surajjha0622/CrashLink/hardware/pcb/gateway_node/2D_gn_top_v1.png

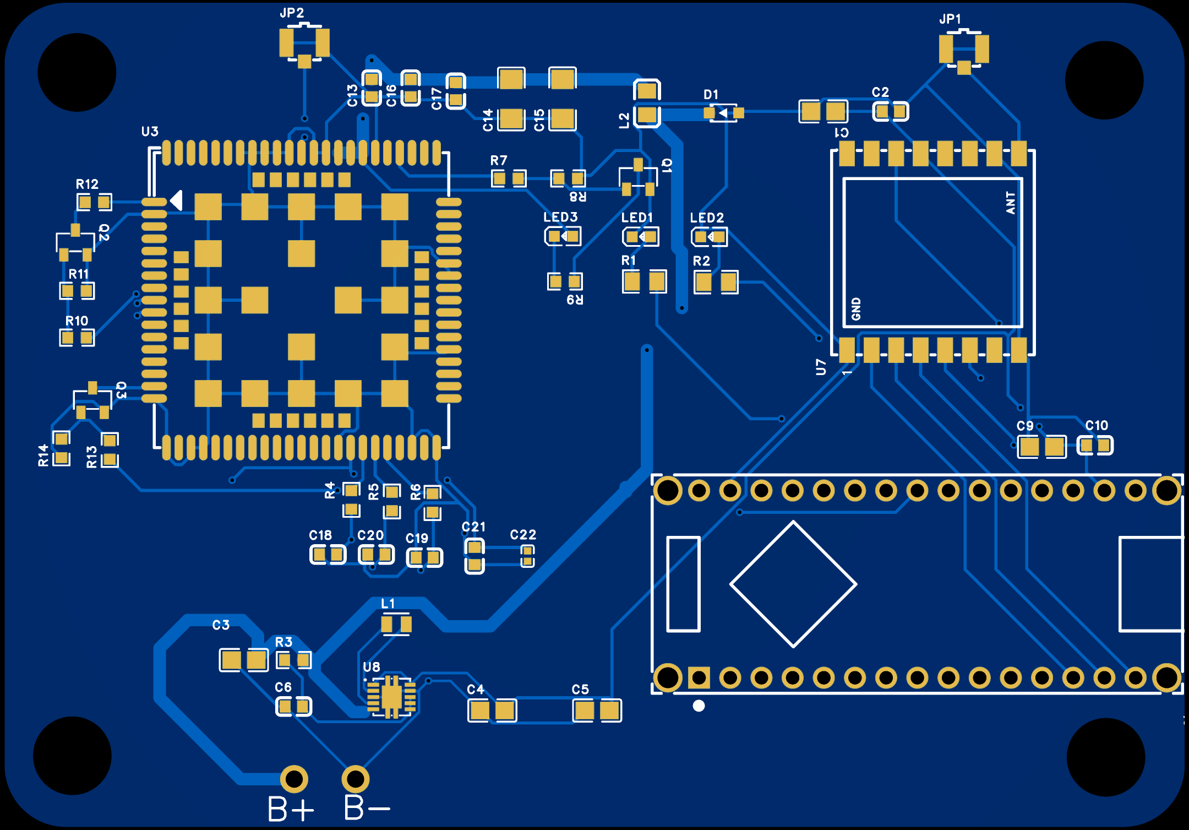
hardware/pcb/gateway_node/2D_gn_top_v1.png
