surajjha0622/CrashLink/hardware/pcb/gateway_node/3D_gn_v1.png

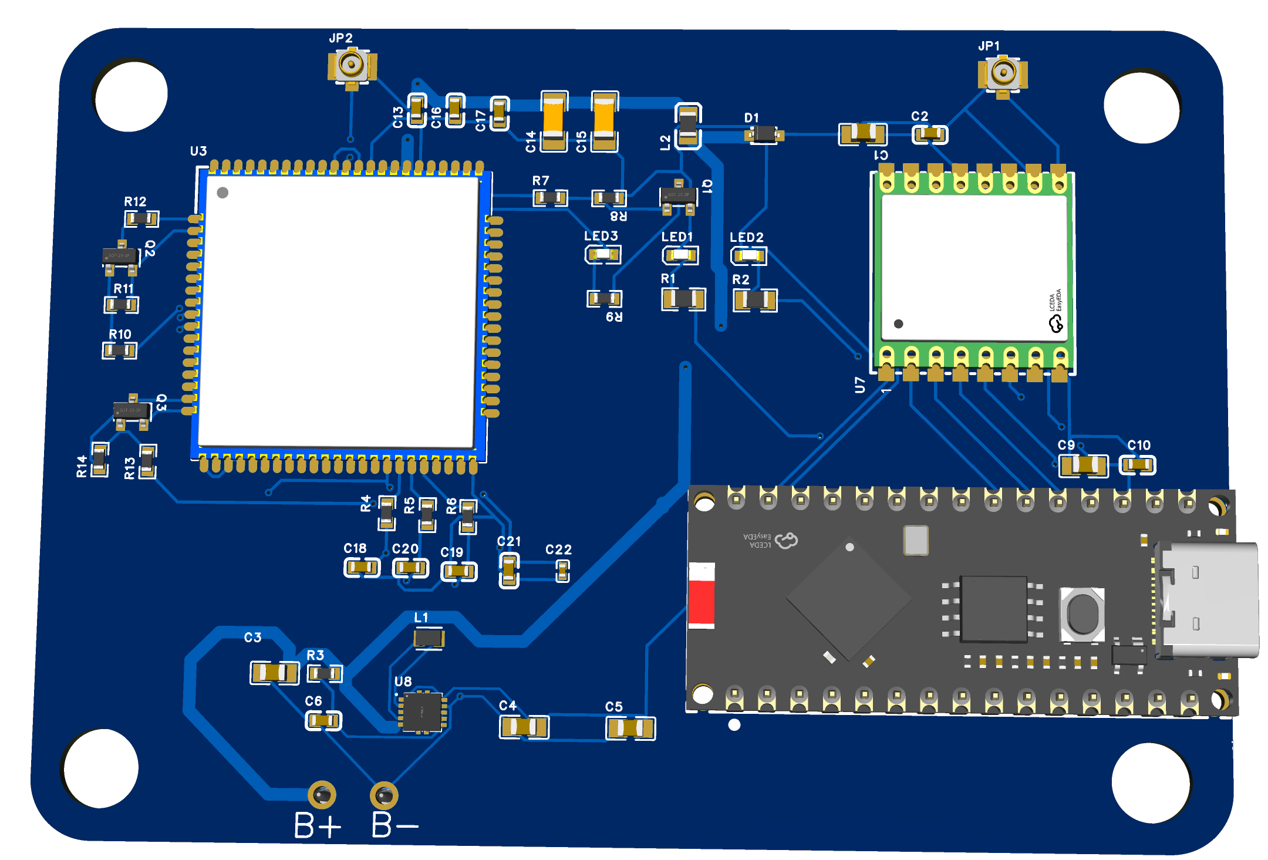
hardware/pcb/gateway_node/3D_gn_v1.png
