surajjha0622/CrashLink/hardware/pcb/gateway_node/PCB_gn_v1.png

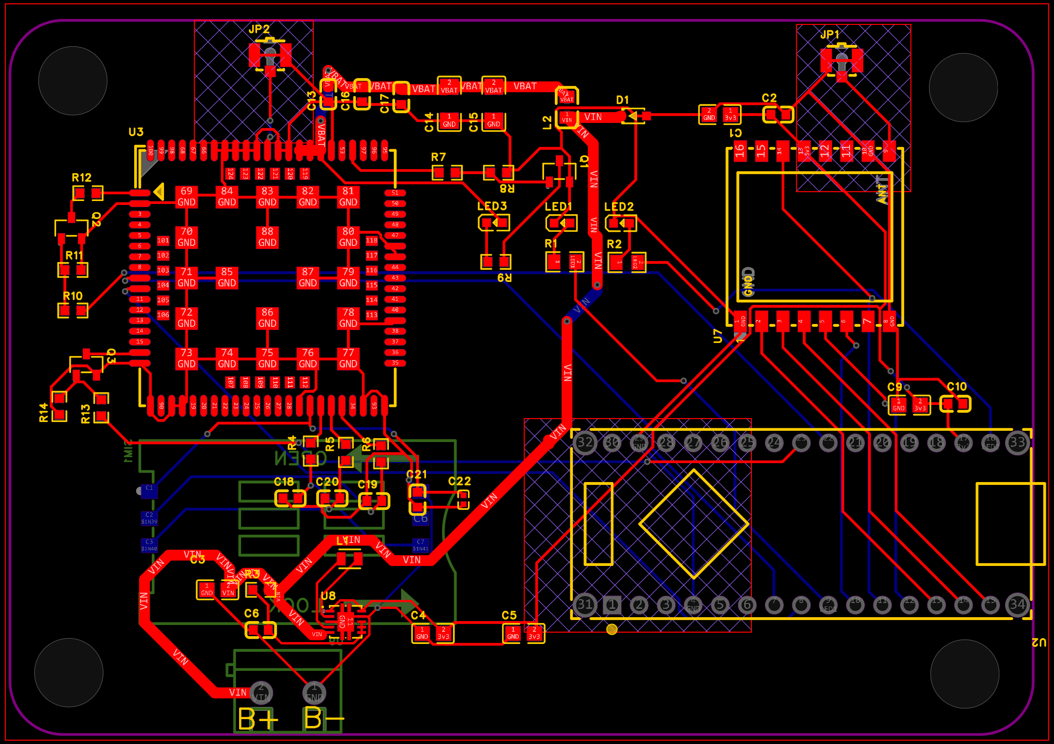
hardware/pcb/gateway_node/PCB_gn_v1.png
