surajjha0622/CrashLink/hardware/pcb/relay_node/2D_rn_bottom_v1.png

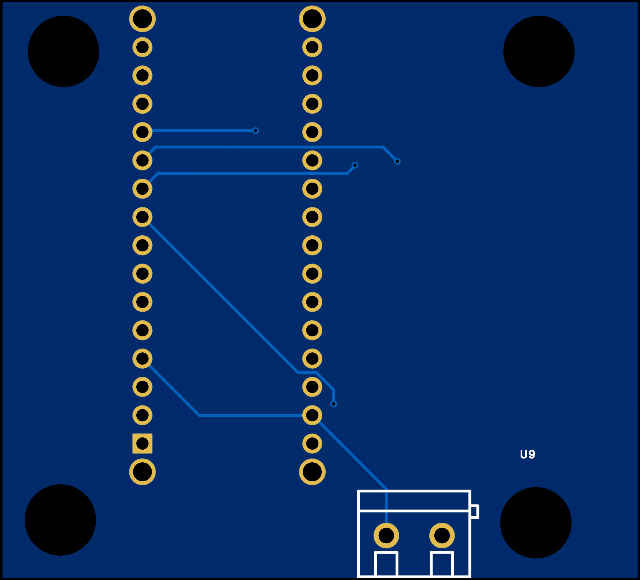
hardware/pcb/relay_node/2D_rn_bottom_v1.png
