surajjha0622/CrashLink/hardware/pcb/relay_node/3D_rn_v1.png

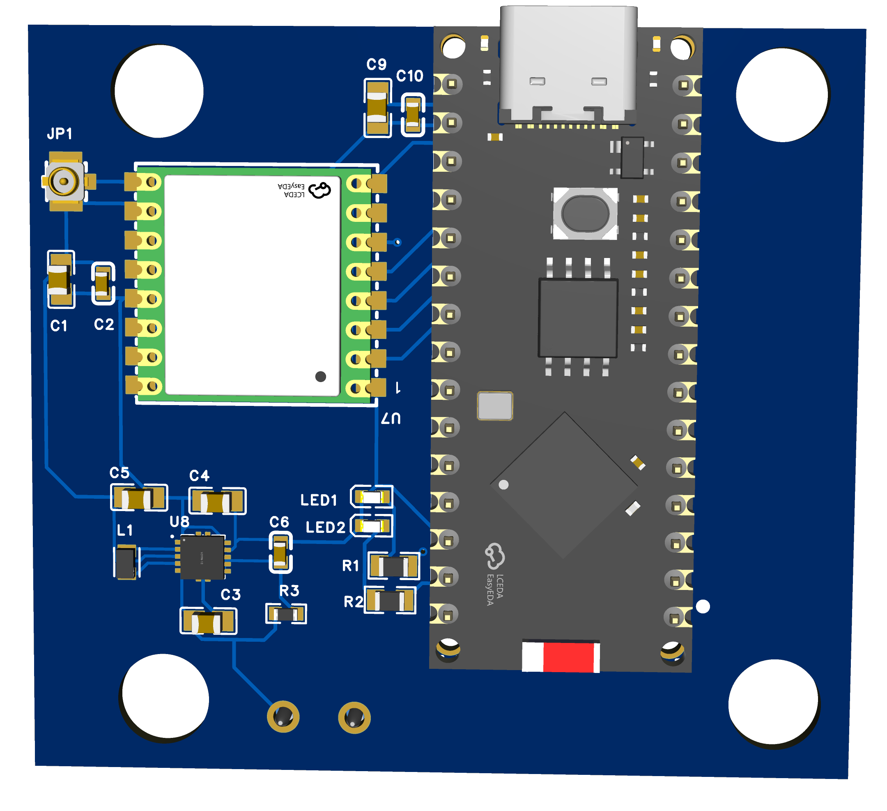
hardware/pcb/relay_node/3D_rn_v1.png
