surajjha0622/CrashLink/hardware/pcb/relay_node/SCH_rn_v1.png

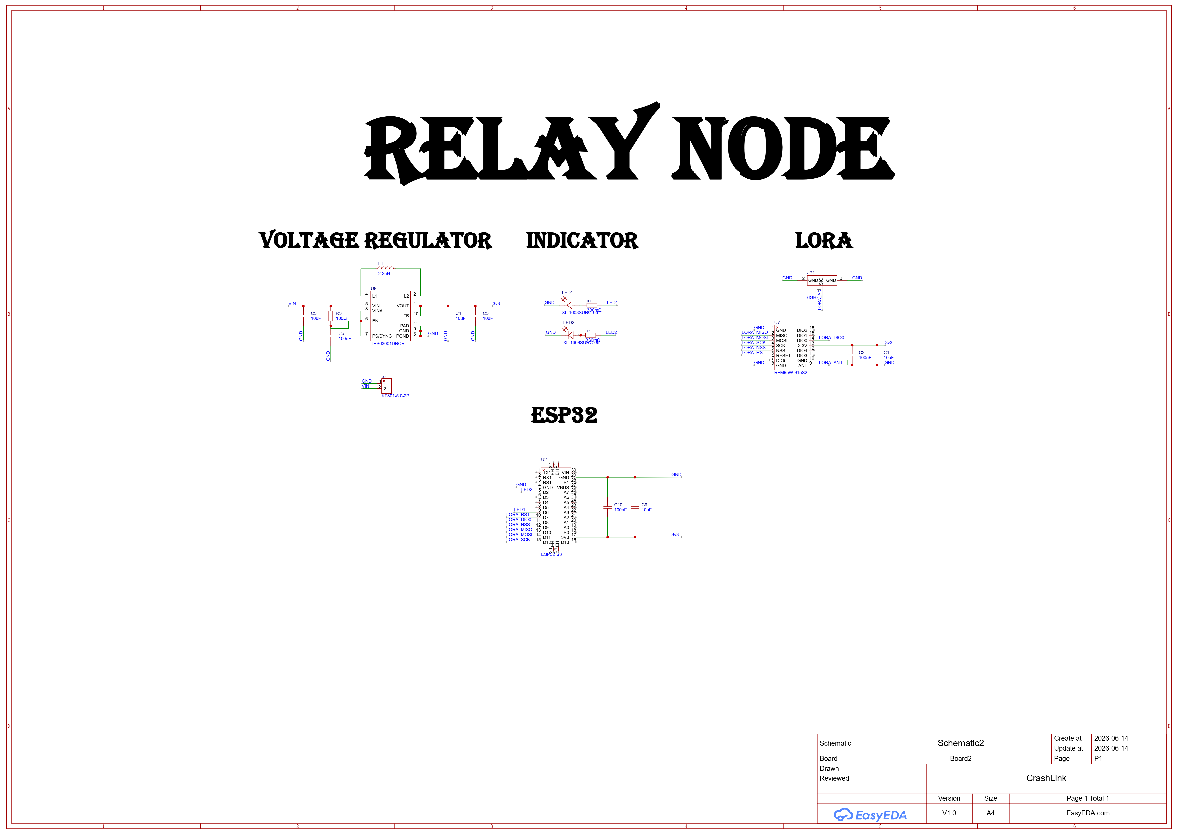
hardware/pcb/relay_node/SCH_rn_v1.png
