surajjha0622/CrashLink/hardware/pcb/vechile_node/2D_vn_top_v1.png

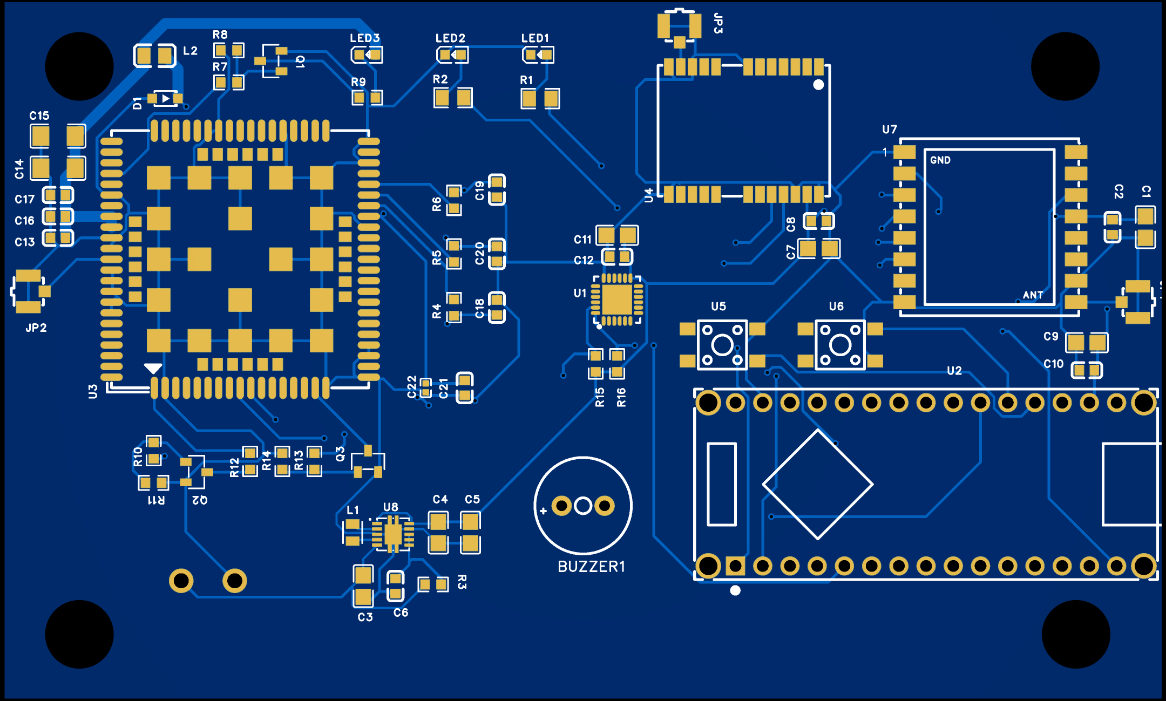
hardware/pcb/vechile_node/2D_vn_top_v1.png
