surajjha0622/CrashLink/hardware/pcb/vechile_node/3D_vn_v1.png

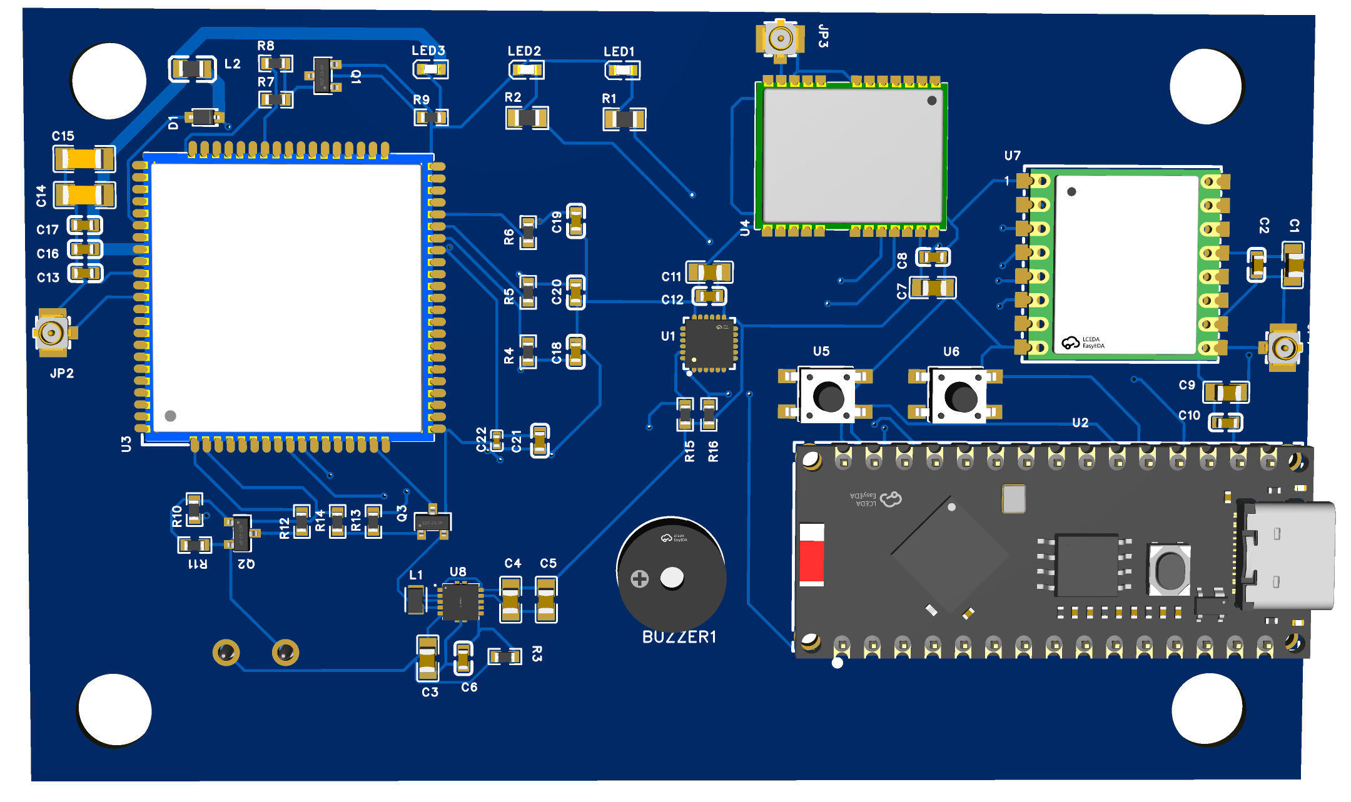
hardware/pcb/vechile_node/3D_vn_v1.png
