surajjha0622/CrashLink/hardware/pcb/vechile_node/PCB_vn_v1.png

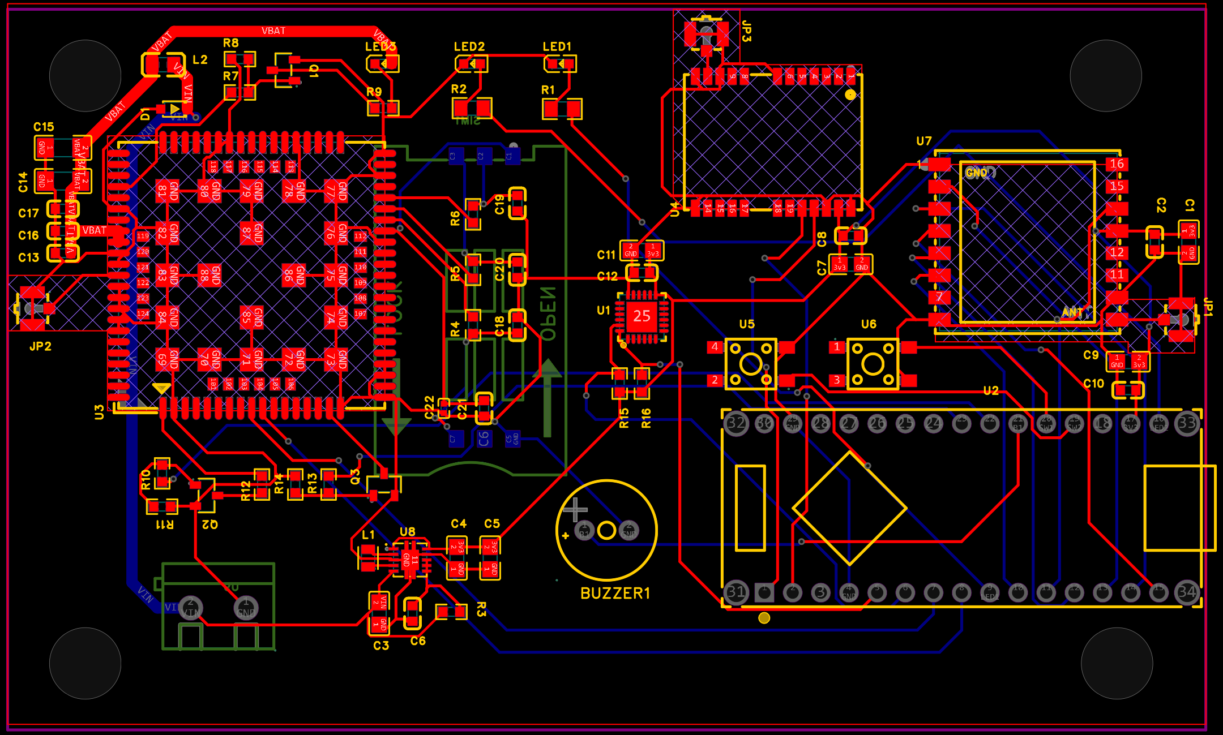
hardware/pcb/vechile_node/PCB_vn_v1.png
