surajjha0622/CrashLink/hardware/pcb/vechile_node/SCH_vn_v1.png

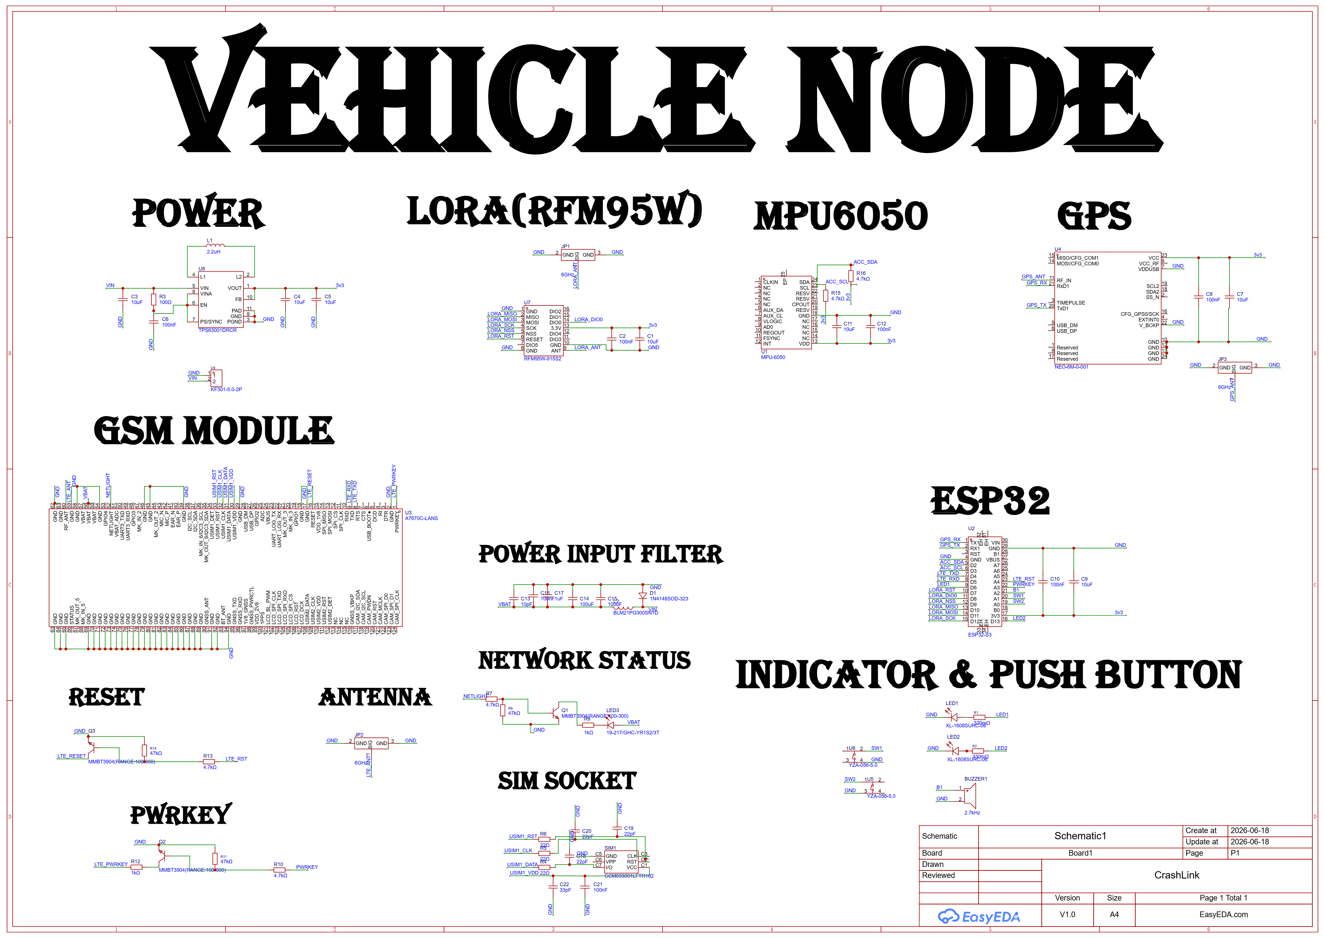
hardware/pcb/vechile_node/SCH_vn_v1.png
