surajjha0622/CrashLink/assets/images/Journal/June7.0.png

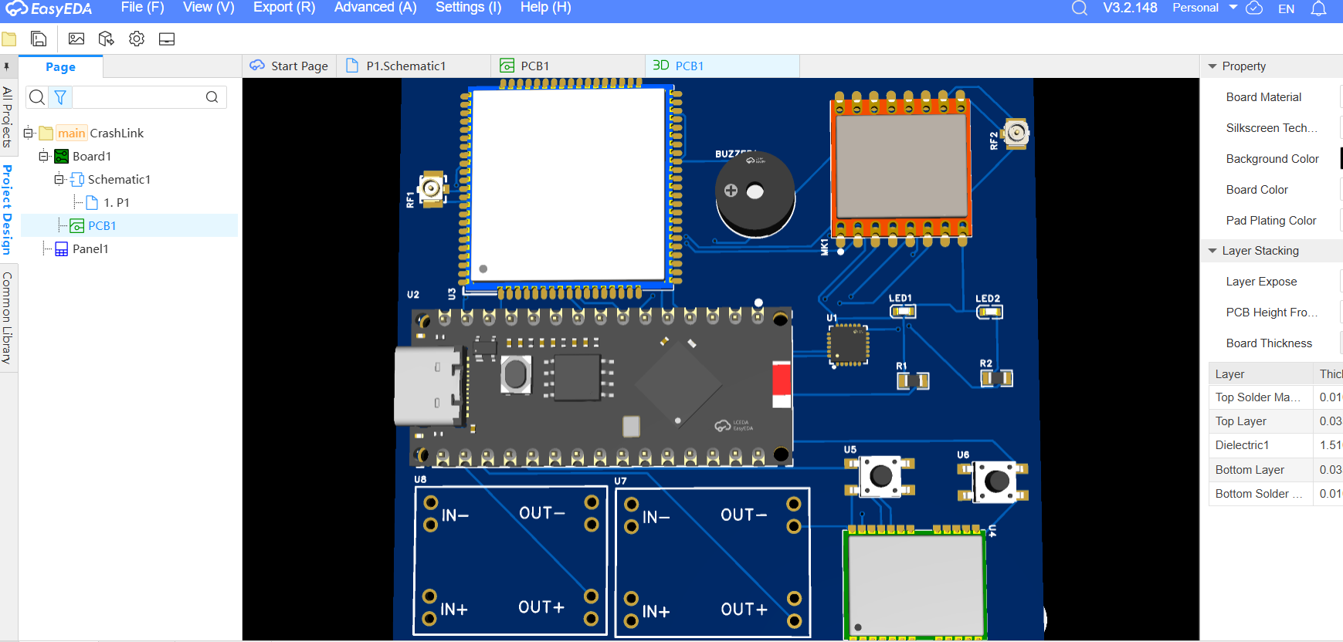
assets/images/Journal/June7.0.png
