surajjha0622/CrashLink/assets/images/Journal/June7.1.png

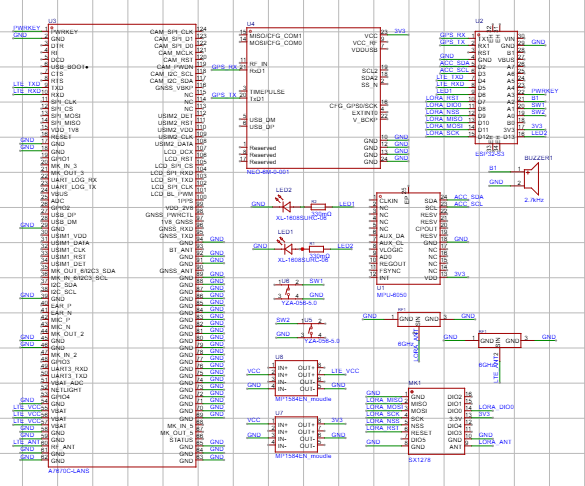
assets/images/Journal/June7.1.png
