surajjha0622/CrashLink/assets/images/Journal/June11.1.jpeg

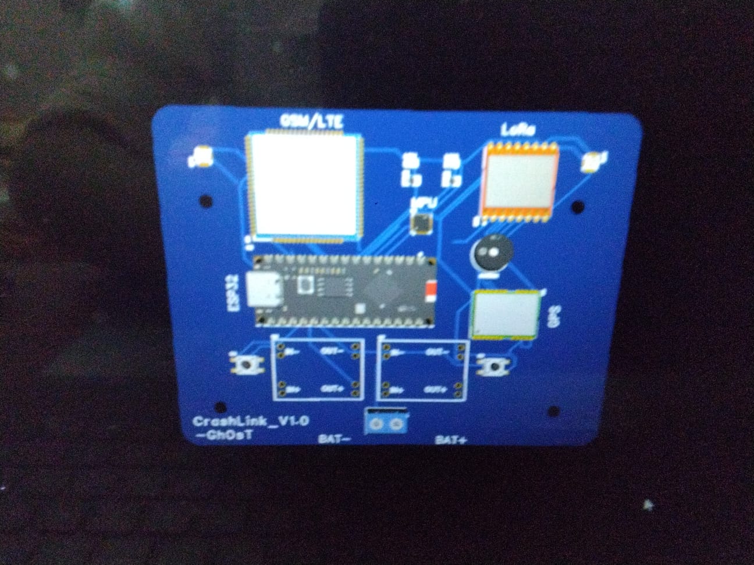
assets/images/Journal/June11.1.jpeg
