surajjha0622/CrashLink/assets/images/Journal/June11.2.jpeg

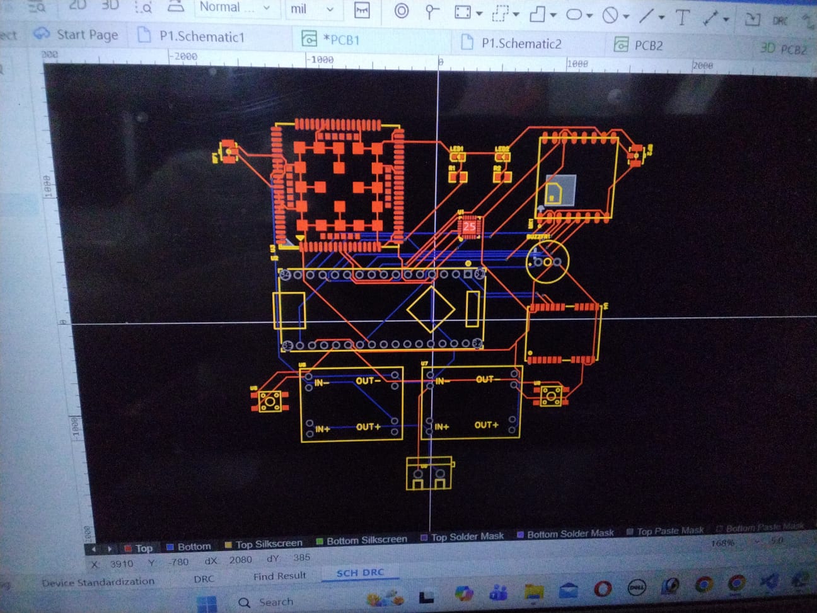
assets/images/Journal/June11.2.jpeg
